Stefan1627/TSC-homework/Hardware/Schematic.sch

## EAGLE design Hardware/Schematic.sch (2026-04-20)

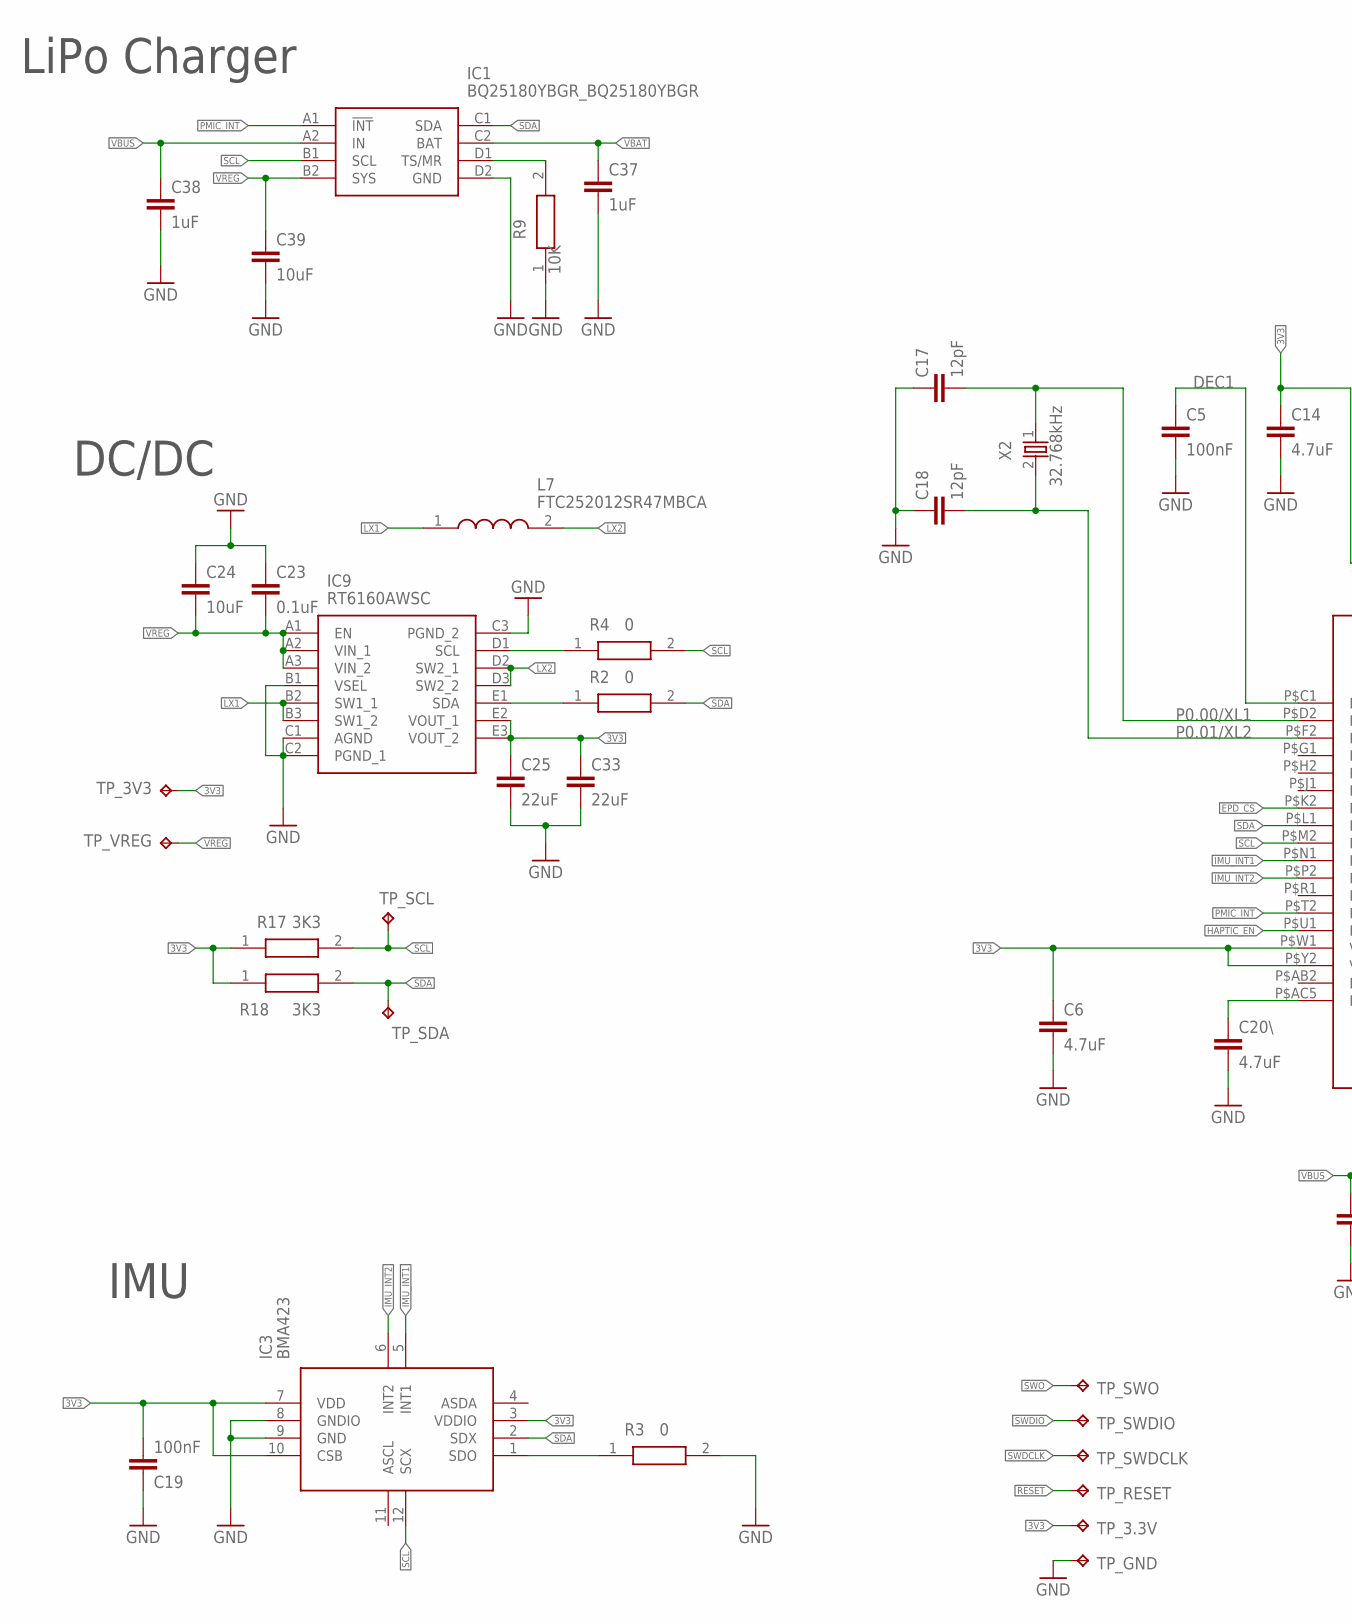
[picture p14: schematic Schematic.sch, sheet 1, part in row 1, column 1]

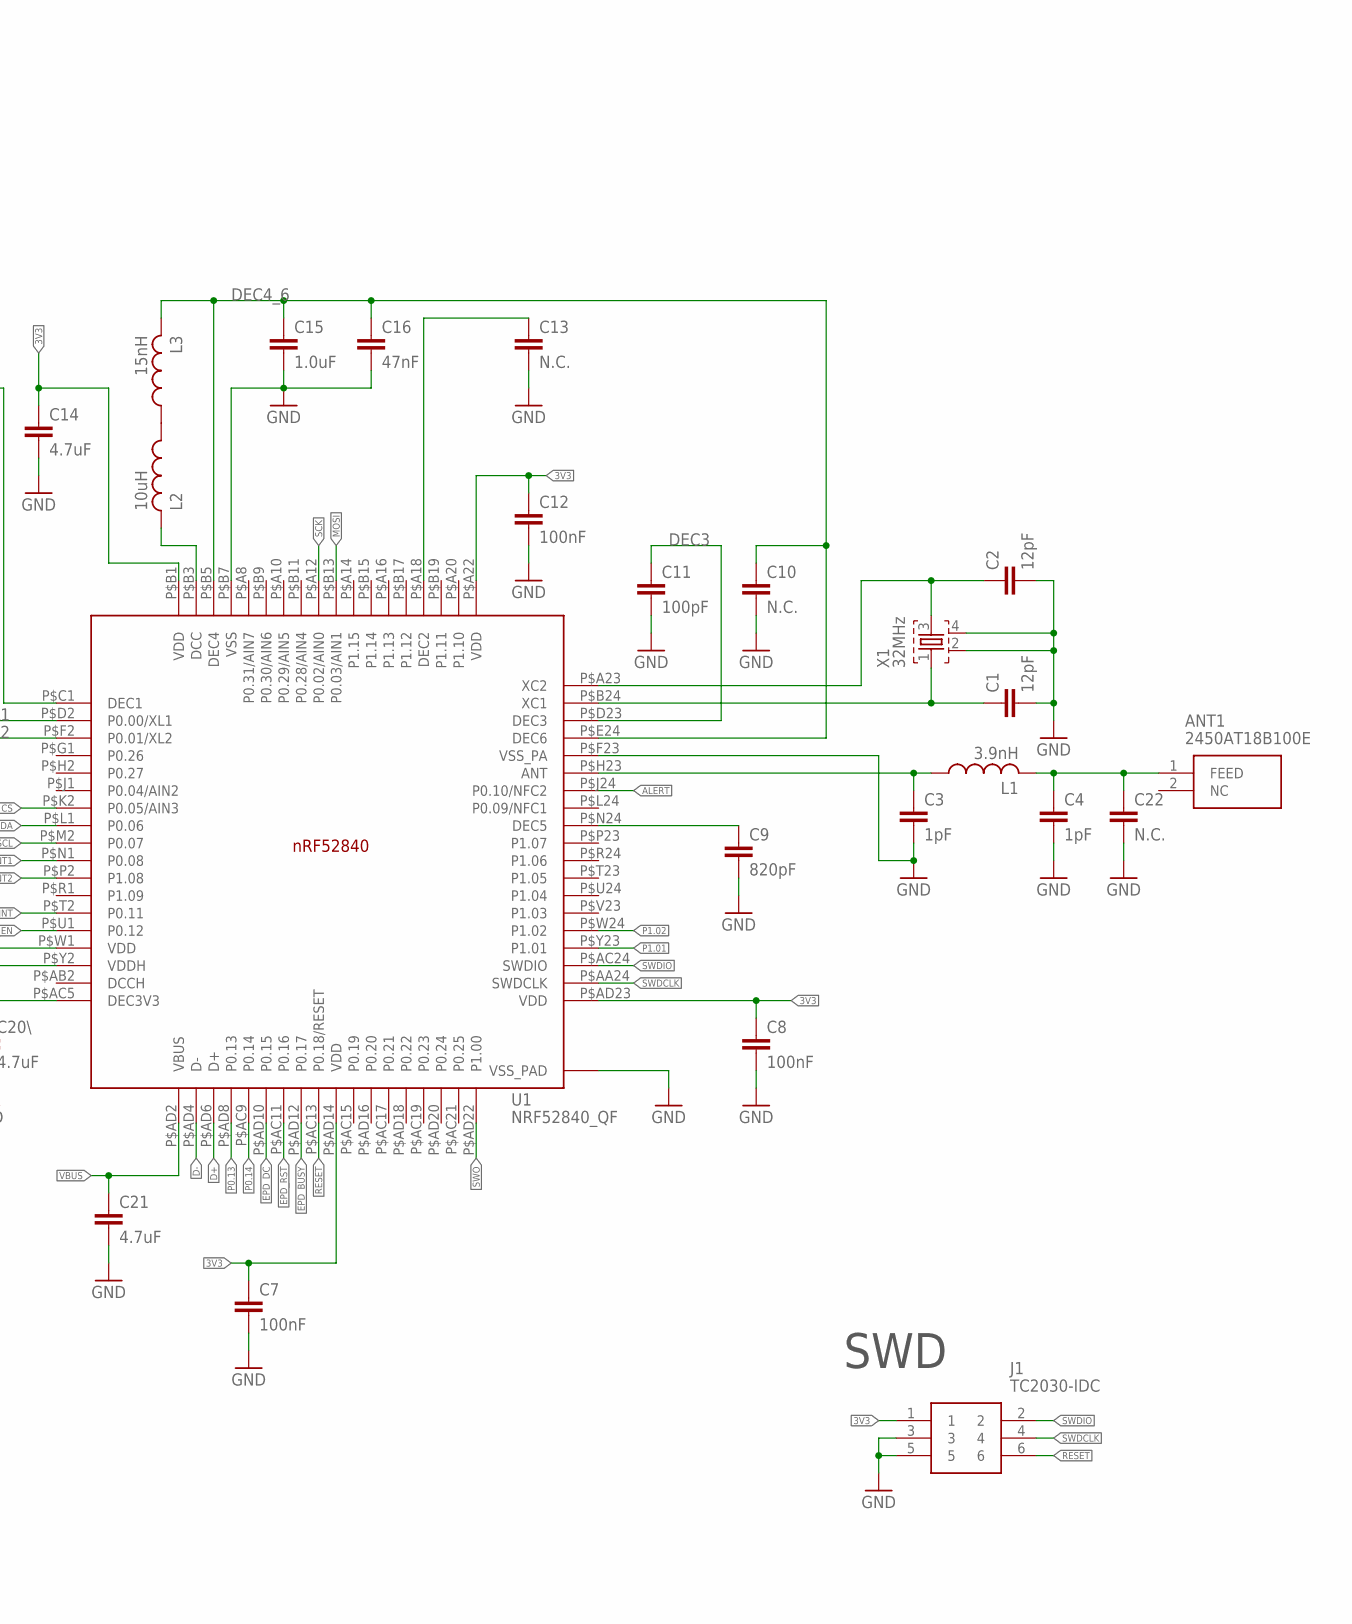
[picture p15: schematic Schematic.sch, sheet 1, part in row 1, column 2]

Parts:
ANT1: 2450AT18B100E; 2450AT18B100E_ANTC3216X140N
C1, C2, C17, C18: 12pF; NORDIC_NRF_3_RESC0201_L
C3, C4: 1pF; NORDIC_NRF_3_RESC0201_L
C5, C7, C8, C12, C19: 100nF; NORDIC_NRF_3_RESC0201_L
C6, C14, C20\, C21: 4.7uF; NORDIC_NRF_3_RESC0402_L
C9: 820pF; NORDIC_NRF_3_RESC0201_L
C10, C13, C22: N.C.; NORDIC_NRF_3_RESC0201_L
C11: 100pF; NORDIC_NRF_3_RESC0201_L
C15: 1.0uF; NORDIC_NRF_3_RESC0402_L
C16: 47nF; NORDIC_NRF_3_RESC0201_L
C23: 0.1uF; NORDIC_NRF_3_RESC0201_L
C24, C39: 10uF; NORDIC_NRF_3_RESC0402_L
C25, C33: 22uF; NORDIC_NRF_3_RESC0402_L
C37, C38: 1uF; NORDIC_NRF_3_RESC0402_L
IC1: BQ25180YBGR_BQ25180YBGR; BQ25180YBGR_BGA8C40P2X4_100X155X50
IC3: BMA423; BMA423_BMA423
IC9: RT6160AWSC; RT6160AWSC_BGA15C40P3X5_140X230X60
J1: TC2030-IDC; TC2030-IDC_TC2030IDC
L1: 3.9nH; NORDIC_NRF_2_RESC0402_L
L2: 10uH; NORDIC_NRF_2_RESC0603_L
L3: 15nH; NORDIC_NRF_2_RESC0402_L
L7: FTC252012SR47MBCA; MLP2016SR47MT0S1_INDC2016X100N
R2, R3, R4: 0; CPF0201D7K68C1_0201
R9: 10K; CPF0201D7K68C1_0201
R17, R18: 3K3; CPF0201D7K68C1_0201
TP_3.3V, TP_3V3: HECTOR_WATCH_1_TPTP20R; HECTOR_WATCH_1_TP20R
TP_GND: HECTOR_WATCH_1_TPTP20R; HECTOR_WATCH_1_TP20R
TP_RESET: HECTOR_WATCH_1_TPTP20R; HECTOR_WATCH_1_TP20R
TP_SCL: HECTOR_WATCH_1_TPTP20R; HECTOR_WATCH_1_TP20R
TP_SDA: HECTOR_WATCH_1_TPTP20R; HECTOR_WATCH_1_TP20R
TP_SWDCLK: HECTOR_WATCH_1_TPTP20R; HECTOR_WATCH_1_TP20R
TP_SWDIO: HECTOR_WATCH_1_TPTP20R; HECTOR_WATCH_1_TP20R
TP_SWO: HECTOR_WATCH_1_TPTP20R; HECTOR_WATCH_1_TP20R
TP_VREG: HECTOR_WATCH_1_TPTP20R; HECTOR_WATCH_1_TP20R
U1: NRF52840_QF; NORDIC_NRF_4_AQFN50P700X700X85_HS-74N
X1: 32MHz; NORDIC_NRF_BT-XTAL_2016_N
X2: 32.768kHz; NORDIC_NRF_1_XTAL_3215_N

Connections:
3V3: C6.1, C7.2, C8.2, C12.2, C14.1, C19.2, C25.1, C33.1, IC3.3 (VDDIO), IC3.7 (VDD), IC3.10 (CSB), IC9.E2 (VOUT_1), IC9.E3 (VOUT_2), J1.1, R17.1, R18.1, TP_3.3V.TP, TP_3V3.TP, U1.P$A22 (VDD), U1.P$AD14 (VDD), U1.P$AD23 (VDD), U1.P$B1 (VDD), U1.P$W1 (VDD), U1.P$Y2 (VDDH)
ALERT: U1.P$J24 (P0.10/NFC2)
D+: U1.P$AD6 (D+)
D-: U1.P$AD4 (D-)
DEC1: C5.2, U1.P$C1 (DEC1)
DEC3: C11.2, U1.P$D23 (DEC3)
DEC4_6: C10.2, C15.1, C16.2, L3.2, U1.P$B5 (DEC4), U1.P$E24 (DEC6)
EPD_BUSY: U1.P$AD12 (P0.17)
EPD_CS: U1.P$K2 (P0.05/AIN3)
EPD_DC: U1.P$AD10 (P0.15)
EPD_RST: U1.P$AC11 (P0.16)
GND: C1.1, C2.2, C3.1, C4.1, C5.1, C6.2, C7.1, C8.1, C9.1, C10.1, C11.1, C12.1, C13.1, C14.2, C15.2, C16.1, C17.1, C18.1, C19.1, C20\.2, C21.2, C22.1, C23.1, C24.1, C25.2, C33.2, C37.2, C38.2, C39.2, IC1.D2 (GND), IC3.8 (GNDIO), IC3.9 (GND), IC9.B1 (VSEL), IC9.C1 (AGND), IC9.C2 (PGND_1), IC9.C3 (PGND_2), J1.3, J1.5, R3.2, R9.1, TP_GND.TP, U1.P$74 (VSS_PAD), U1.P$B7 (VSS), U1.P$F23 (VSS_PA), X1.2, X1.4
HAPTIC_EN: U1.P$U1 (P0.12)
IMU_INT1: IC3.5 (INT1), U1.P$N1 (P0.08)
IMU_INT2: IC3.6 (INT2), U1.P$P2 (P1.08)
LX1: IC9.B2 (SW1_1), IC9.B3 (SW1_2), L7.1
LX2: IC9.D2 (SW2_1), IC9.D3 (SW2_2), L7.2
MOSI: U1.P$B13 (P0.03/AIN1)
unnamed: IC9.E1 (SDA), R2.1
unnamed: IC1.D1 (TS/MR), R9.2
unnamed: IC9.D1 (SCL), R4.1
unnamed: C9.2, U1.P$N24 (DEC5)
unnamed: IC3.1 (SDO), R3.1
unnamed: C1.2, U1.P$B24 (XC1), X1.1
unnamed: C3.2, L1.1, U1.P$H23 (ANT)
unnamed: L2.1, L3.1
unnamed: C13.2, U1.P$A18 (DEC2)
unnamed: L2.2, U1.P$B3 (DCC)
unnamed: C20\.1, U1.P$AC5 (DEC3V3)
unnamed: C2.1, U1.P$A23 (XC2), X1.3
P0.00/XL1: C17.2, U1.P$D2 (P0.00/XL1), X2.1
P0.01/XL2: C18.2, U1.P$F2 (P0.01/XL2), X2.2
P0.13: U1.P$AD8 (P0.13)
P0.14: U1.P$AC9 (P0.14)
P1.01: U1.P$Y23 (P1.01)
P1.02: U1.P$W24 (P1.02)
PMIC_INT: IC1.A1 (!INT), U1.P$T2 (P0.11)
RESET: J1.6, TP_RESET.TP, U1.P$AC13 (P0.18/RESET)
RF: ANT1.1 (FEED), C4.2, C22.2, L1.2
SCK: U1.P$A12 (P0.02/AIN0)
SCL: IC1.B1 (SCL), IC3.12 (SCX), R4.2, R17.2, TP_SCL.TP, U1.P$M2 (P0.07)
SDA: IC1.C1 (SDA), IC3.2 (SDX), R2.2, R18.2, TP_SDA.TP, U1.P$L1 (P0.06)
SWDCLK: J1.4, TP_SWDCLK.TP, U1.P$AA24 (SWDCLK)
SWDIO: J1.2, TP_SWDIO.TP, U1.P$AC24 (SWDIO)
SWO: TP_SWO.TP, U1.P$AD22 (P1.00)
VBAT: C37.1, IC1.C2 (BAT)
VBUS: C21.1, C38.1, IC1.A2 (IN), U1.P$AD2 (VBUS)
VREG: C23.2, C24.2, C39.1, IC1.B2 (SYS), IC9.A1 (EN), IC9.A2 (VIN_1), IC9.A3 (VIN_2), TP_VREG.TP

Notes on the sheet:
LiPo Charger
DC/DC
IMU
SWD
