Stefan1627/TSC-homework/Hardware/Schematic.sch

## EAGLE design Hardware/Schematic.sch (continued)

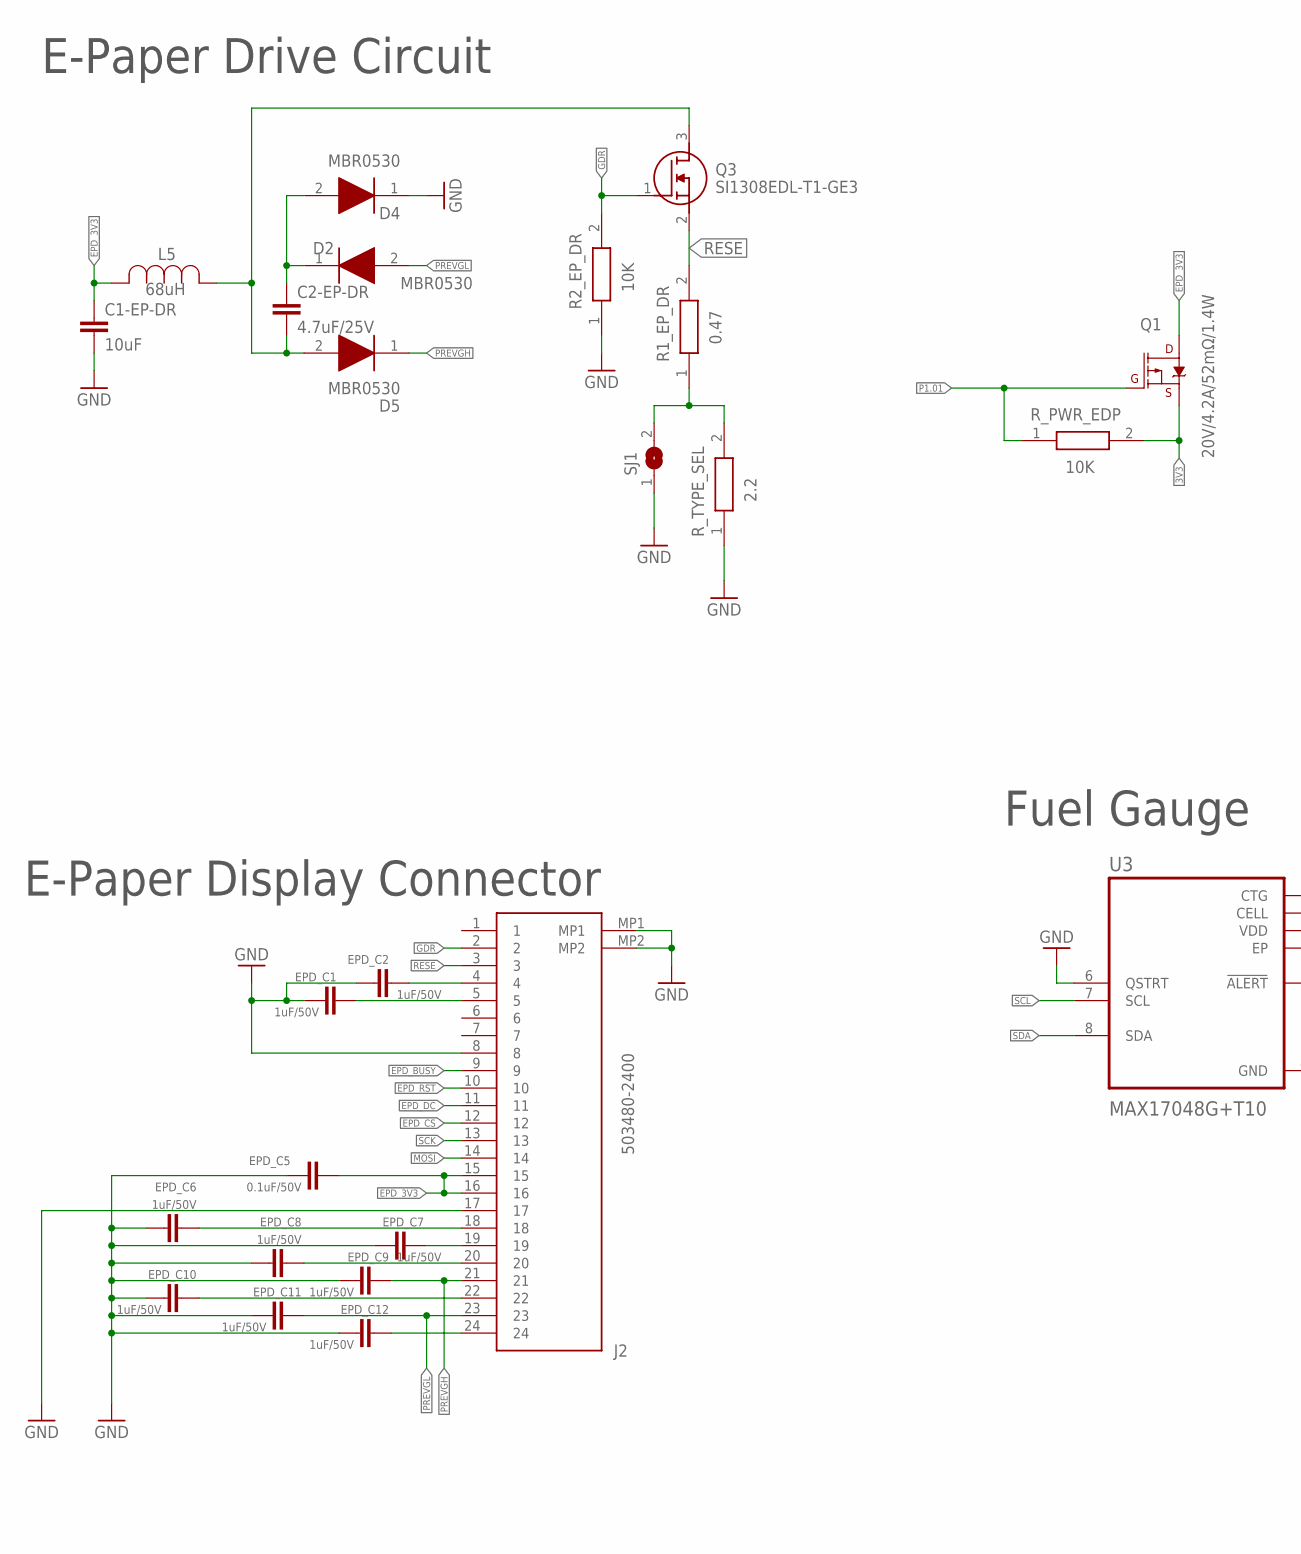
[picture p16: schematic Schematic.sch, sheet 2, part in row 1, column 1]

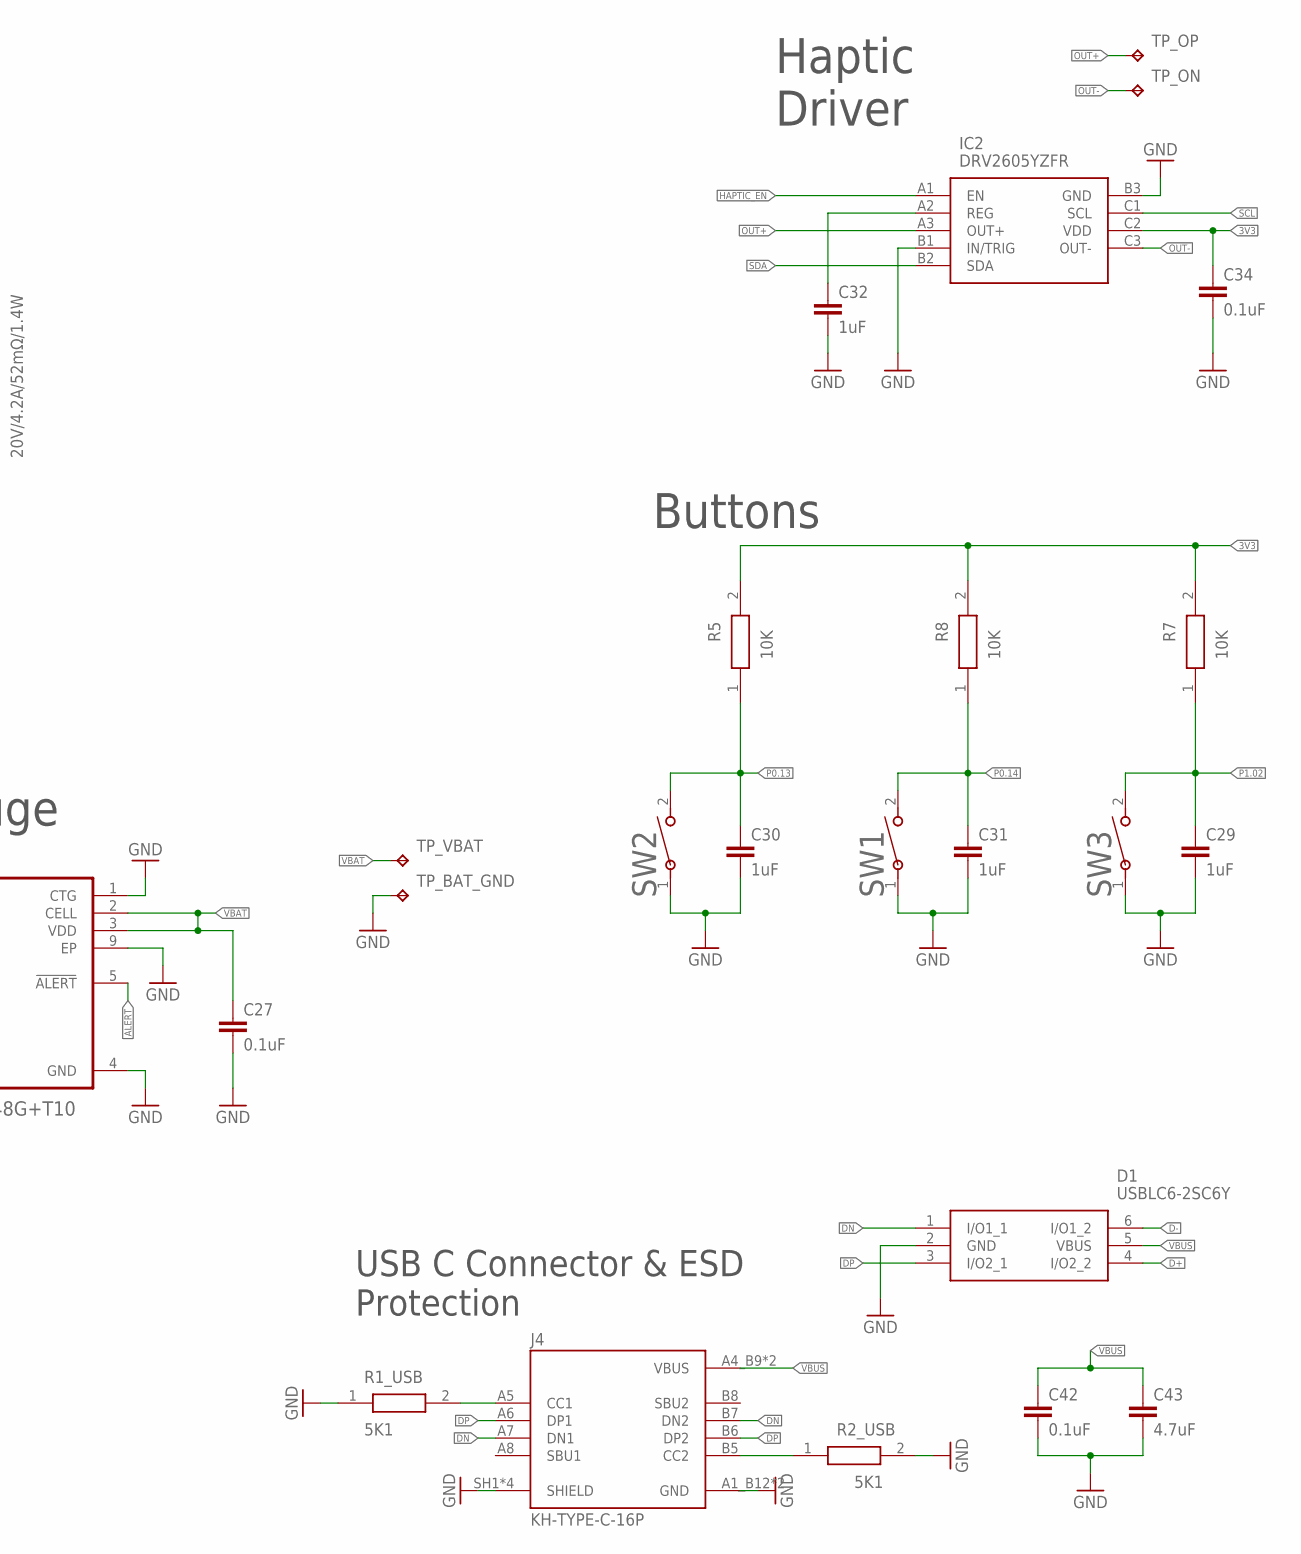
[picture p17: schematic Schematic.sch, sheet 2, part in row 1, column 2]

Parts:
C1-EP-DR: 10uF; NORDIC_NRF_3_RESC0402_L
C2-EP-DR: 4.7uF/25V; NORDIC_NRF_3_RESC0402_L
C27, C34, C42: 0.1uF; NORDIC_NRF_3_RESC0201_L
C29, C30, C31, C32: 1uF; NORDIC_NRF_3_RESC0402_L
C43: 4.7uF; NORDIC_NRF_3_RESC0402_L
D1: USBLC6-2SC6Y; SOT95P280X145-6N
D2, D4, D5: MBR0530; ESP32_C6_LIBRARY_5_SOD3716X135N
EPD_C1, EPD_C2, EPD_C6, EPD_C7, EPD_C8, EPD_C9, EPD_C10, EPD_C11, EPD_C12: 1uF/50V; NORDIC_NRF_3_RESC0402_L
EPD_C5: 0.1uF/50V; NORDIC_NRF_3_RESC0402_L
IC2: DRV2605YZFR; DRV2605YZFR_BGA9C50P3X3_144X144X62
J2: 503480-2400; 503480-2400_5034802400
J4: KH-TYPE-C-16P; KH-TYPE-C-16P_KINGHELM_KH-TYPE-C-16P
L5: 68uH; ESP32_C6_LIBRARY_2_IND_4828-WE-TPC_WRE
Q1: 20V/4.2A/52mΩ/1.4W; ESP32_C6_LIBRARY_4_ESP32_C6_LIBRARY_4_ESP32_C6_LIBRARY_4_ES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
Q3: SI1308EDL-T1-GE3; ESP32_C6_LIBRARY_6_SOT65P210X110-3N
R1_EP_DR: 0.47; CPF0201D7K68C1_0201
R1_USB, R2_USB: 5K1; CPF0201D7K68C1_0201
R2_EP_DR, R5, R7, R8: 10K; CPF0201D7K68C1_0201
R_PWR_EDP: 10K; CPF0201D7K68C1_0201
R_TYPE_SEL: 2.2; CPF0201D7K68C1_0201
SJ1: ESP32_C6_LIBRARY_7_JUMPER_SJ
SW1, SW2, SW3: 2025-10-22_07-23-44_LIBRARY_EVP-AKE31ASW_EVP-AKE3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; 2025-10-22_07-23-44_LIBRARY_SW_EVP-AKE31A_PAN
TP_BAT_GND: HECTOR_WATCH_1_TPTP20R; HECTOR_WATCH_1_TP20R
TP_ON: HECTOR_WATCH_1_TPTP20R; HECTOR_WATCH_1_TP20R
TP_OP: HECTOR_WATCH_1_TPTP20R; HECTOR_WATCH_1_TP20R
TP_VBAT: HECTOR_WATCH_1_TPTP20R; HECTOR_WATCH_1_TP20R
U3: MAX17048G+T10; ESP32_C6_LIBRARY_SON50P200X200X80-9N

Connections:
3V3: C34.1, IC2.C2 (VDD), Q1.2 (S), R5.2, R7.2, R8.2, R_PWR_EDP.2
ALERT: U3.5 (!ALERT)
D+: D1.4 (I/O2_2)
D-: D1.6 (I/O1_2)
DN: D1.1 (I/O1_1), J4.A7 (DN1), J4.B7 (DN2)
DP: D1.3 (I/O2_1), J4.A6 (DP1), J4.B6 (DP2)
EPD_3V3: C1-EP-DR.1, EPD_C5.2, J2.15, J2.16, L5.2, Q1.3 (D)
EPD_BUSY: J2.9
EPD_CS: J2.12
EPD_DC: J2.11
EPD_RST: J2.10
GDR: J2.2, Q3.1 (G), R2_EP_DR.2
GND: C1-EP-DR.2, C27.2, C29.2, C30.2, C31.2, C32.2, C34.2, C42.2, C43.2, D1.2 (GND), D4.1 (K), EPD_C1.1, EPD_C2.1, EPD_C5.1, EPD_C6.1, EPD_C7.1, EPD_C8.1, EPD_C9.1, EPD_C10.1, EPD_C11.1, EPD_C12.1, IC2.B1 (IN/TRIG), IC2.B3 (GND), J2.8, J2.17, J2.MP1, J2.MP2, J4.A1_B12 (GND), J4.SH1 (SHIELD), R1_USB.1, R2_EP_DR.1, R2_USB.2, R_TYPE_SEL.1, SJ1.1, SW1.1, SW2.1, SW3.1, TP_BAT_GND.TP, U3.1 (CTG), U3.4 (GND), U3.6 (QSTRT), U3.9 (EP)
HAPTIC_EN: IC2.A1 (EN)
MOSI: J2.14
unnamed: C2-EP-DR.2, D5.2 (A), L5.1, Q3.3 (D)
unnamed: R1_EP_DR.1, R_TYPE_SEL.2, SJ1.2
unnamed: C2-EP-DR.1, D2.1 (K), D4.2 (A)
unnamed: EPD_C2.2, J2.4
unnamed: EPD_C1.2, J2.5
unnamed: C32.1, IC2.A2 (REG)
unnamed: EPD_C6.2, J2.18
unnamed: EPD_C7.2, J2.19
unnamed: EPD_C8.2, J2.20
unnamed: J4.B5 (CC2), R2_USB.1
unnamed: EPD_C10.2, J2.22
unnamed: EPD_C12.2, J2.24
unnamed: J4.A5 (CC1), R1_USB.2
OUT+: IC2.A3 (OUT+), TP_OP.TP
OUT-: IC2.C3 (OUT-), TP_ON.TP
P0.13: C30.1, R5.1, SW2.2
P0.14: C31.1, R8.1, SW1.2
P1.01: Q1.1 (G), R_PWR_EDP.1
P1.02: C29.1, R7.1, SW3.2
PREVGH: D5.1 (K), EPD_C9.2, J2.21
PREVGL: D2.2 (A), EPD_C11.2, J2.23
RESE: J2.3, Q3.2 (S), R1_EP_DR.2
SCK: J2.13
SCL: IC2.C1 (SCL), U3.7 (SCL)
SDA: IC2.B2 (SDA), U3.8 (SDA)
VBAT: C27.1, TP_VBAT.TP, U3.2 (CELL), U3.3 (VDD)
VBUS: C42.1, C43.1, D1.5 (VBUS), J4.A4_B9 (VBUS)

Notes on the sheet:
E-Paper Drive Circuit
Haptic Driver
Buttons
USB C Connector & ESD Protection
Fuel Gauge
E-Paper Display Connector
